jmk0/rome/img/sensor.jpg

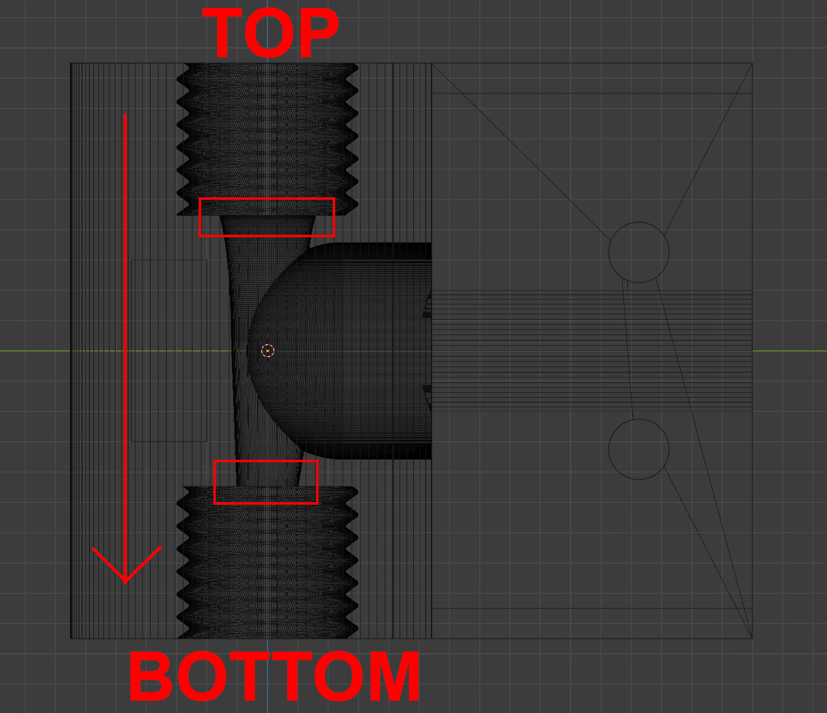
img/sensor.jpg
